Borval99/EBmetro/3D Model/Display Legno/Back.SLDPRT

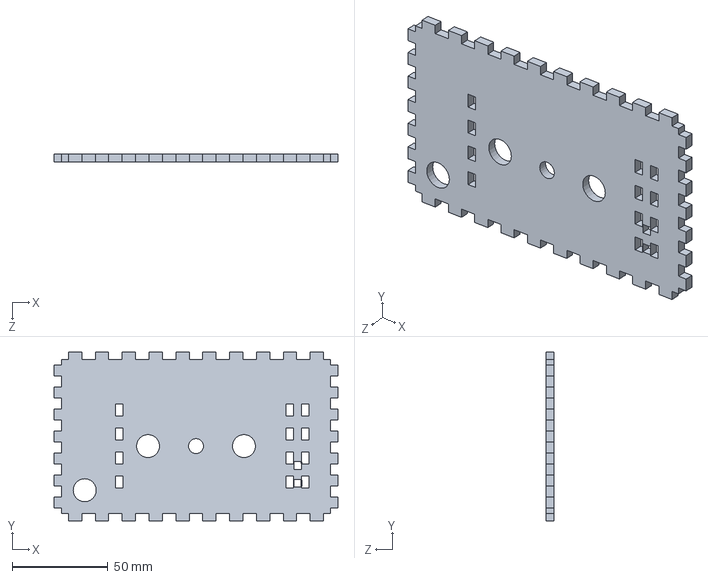
[picture p22: CAD file, 2026-04-02]
3D Model/Display Legno/Back.SLDPRT
148.0 x 88.0 x 4.00 mm
