Borval99/EBmetro/3D Model/Display/Encoder.SLDPRT

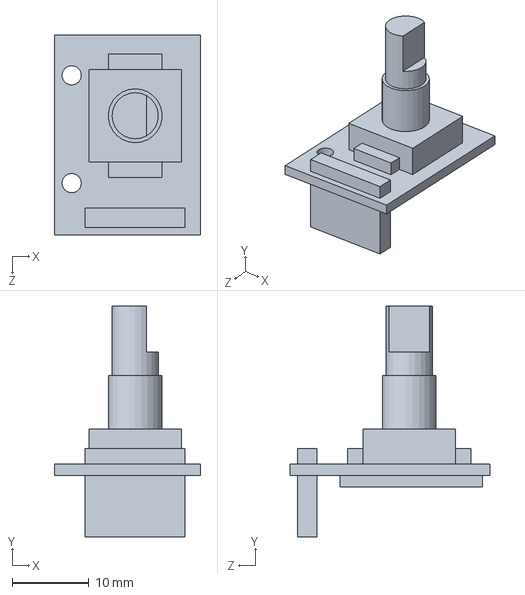
[picture p23: CAD file, 2026-04-02]
3D Model/Display/Encoder.SLDPRT
19.0 x 30.0 x 26.0 mm
