Borval99/EBmetro/3D Model/Display Legno/Left.SLDPRT

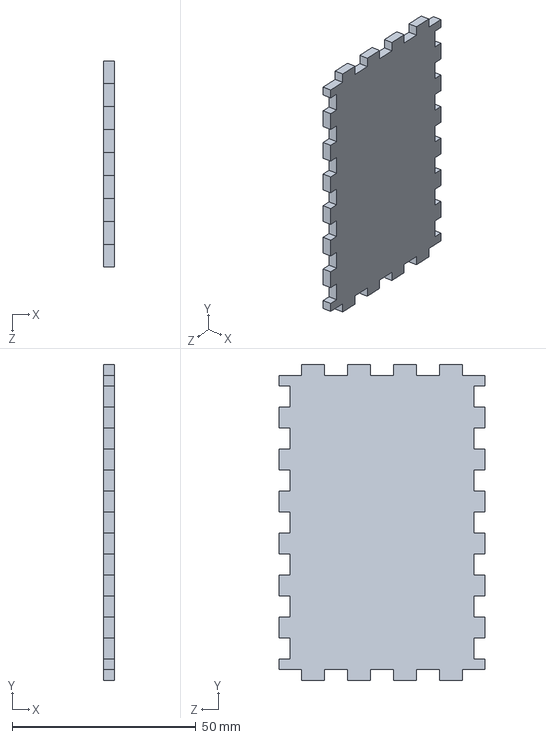
[picture p24: CAD file, 2026-04-02]
3D Model/Display Legno/Left.SLDPRT
3.00 x 86.0 x 56.0 mm
