Borval99/EBmetro/3D Model/Display/MKR1010WiFi.SLDPRT

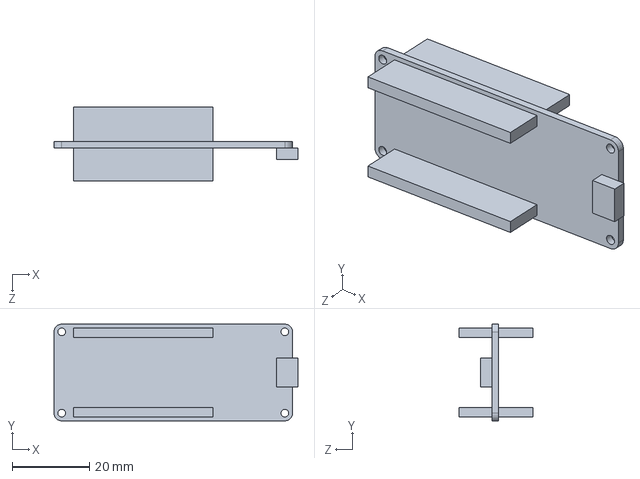
[picture p25: CAD file, 2026-04-02]
3D Model/Display/MKR1010WiFi.SLDPRT
63.0 x 25.0 x 19.2 mm
