Borval99/EBmetro/3D Model/Display Legno/RightV3.SLDPRT

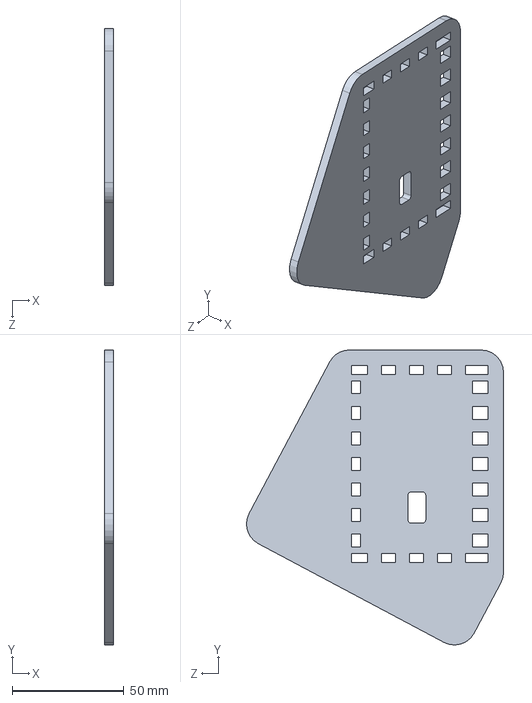
[picture p26: CAD file, 2026-04-02]
3D Model/Display Legno/RightV3.SLDPRT
4.00 x 132.0 x 115.1 mm
