Borval99/EBmetro/3D Model/Display/Case_Base.SLDPRT

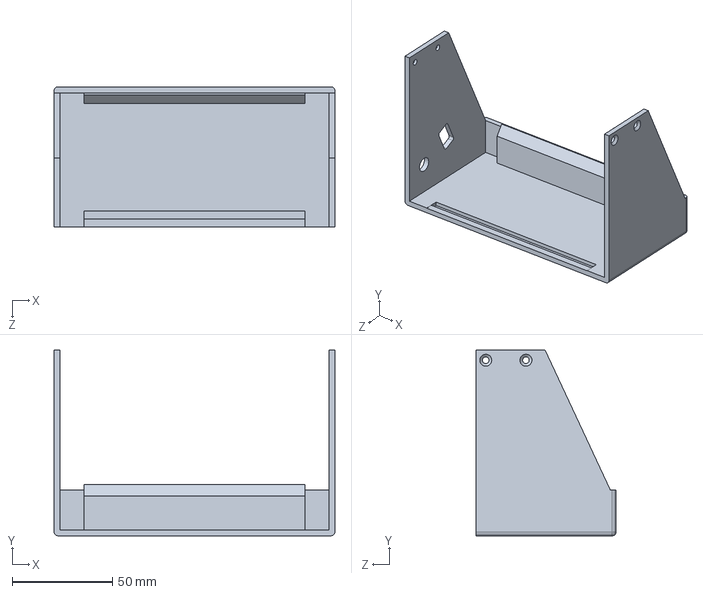
[picture p27: CAD file, 2026-04-02]
3D Model/Display/Case_Base.SLDPRT
140.0 x 92.5 x 70.0 mm
