Borval99/EBmetro/3D Model/Display Legno/Boccola_4.SLDPRT

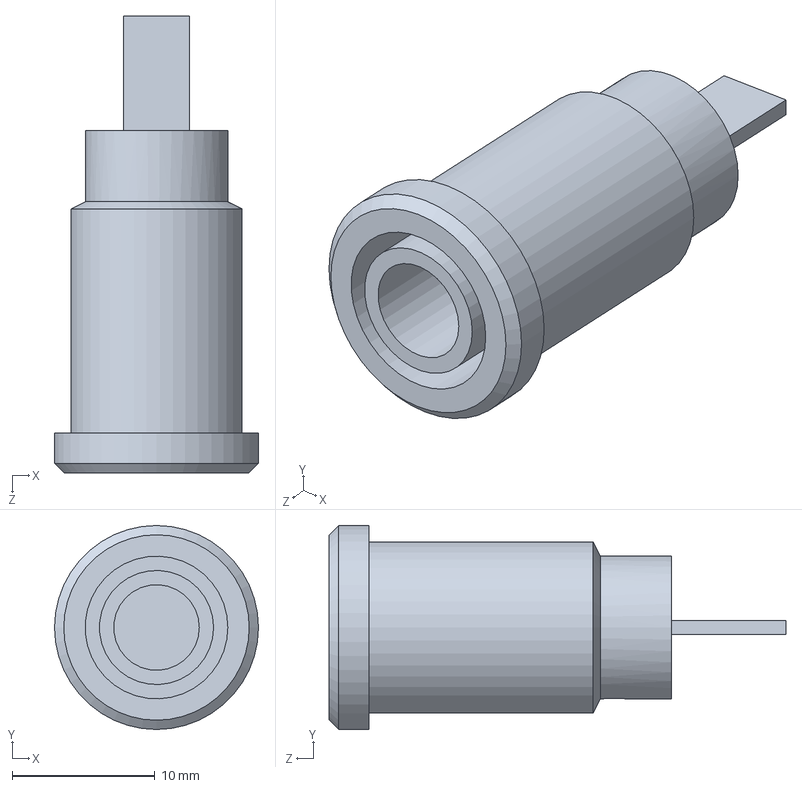
[picture p28: CAD file, 2026-04-02]
3D Model/Display Legno/Boccola_4.SLDPRT
14.3 x 14.3 x 32.0 mm
