Borval99/EBmetro/3D Model/Display Legno/Front.SLDPRT

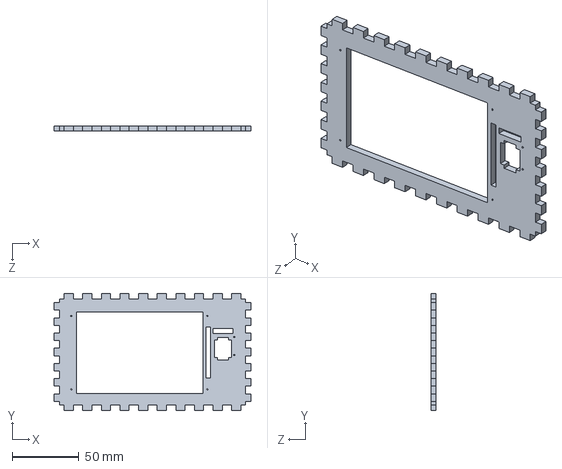
[picture p29: CAD file, 2026-04-02]
3D Model/Display Legno/Front.SLDPRT
148.0 x 88.0 x 4.00 mm
