Borval99/EBmetro/3D Model/Display Legno/Pirulino.SLDPRT

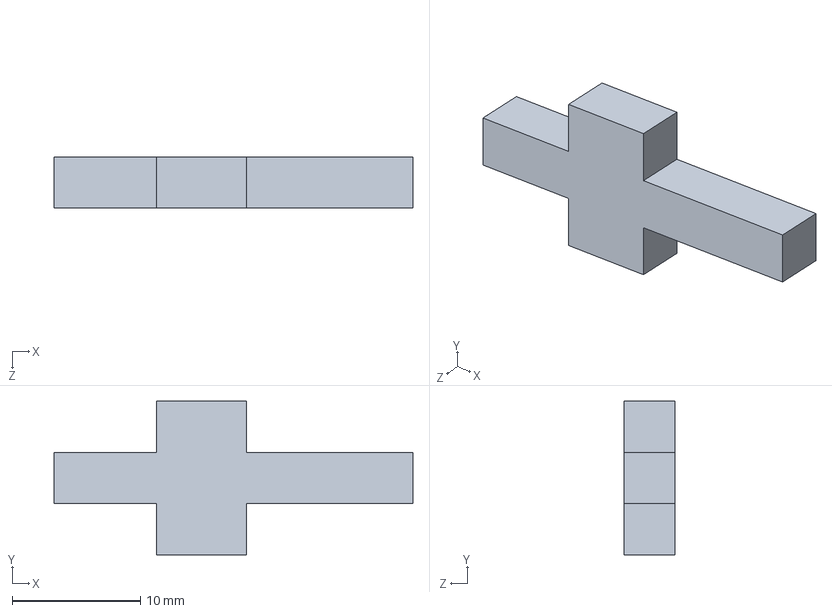
[picture p30: CAD file, 2026-04-02]
3D Model/Display Legno/Pirulino.SLDPRT
28.0 x 12.0 x 4.00 mm
