Borval99/EBmetro/3D Model/Display Legno/PW_Conn.SLDPRT

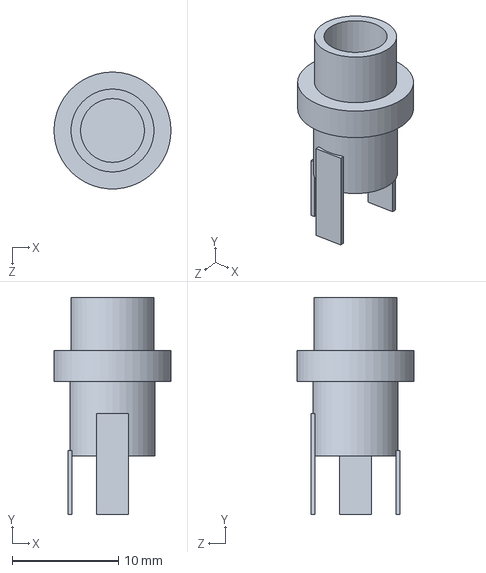
[picture p31: CAD file, 2026-04-02]
3D Model/Display Legno/PW_Conn.SLDPRT
11.0 x 20.4 x 11.0 mm
