Borval99/EBmetro/3D Model/Display Legno/Mask.SLDPRT

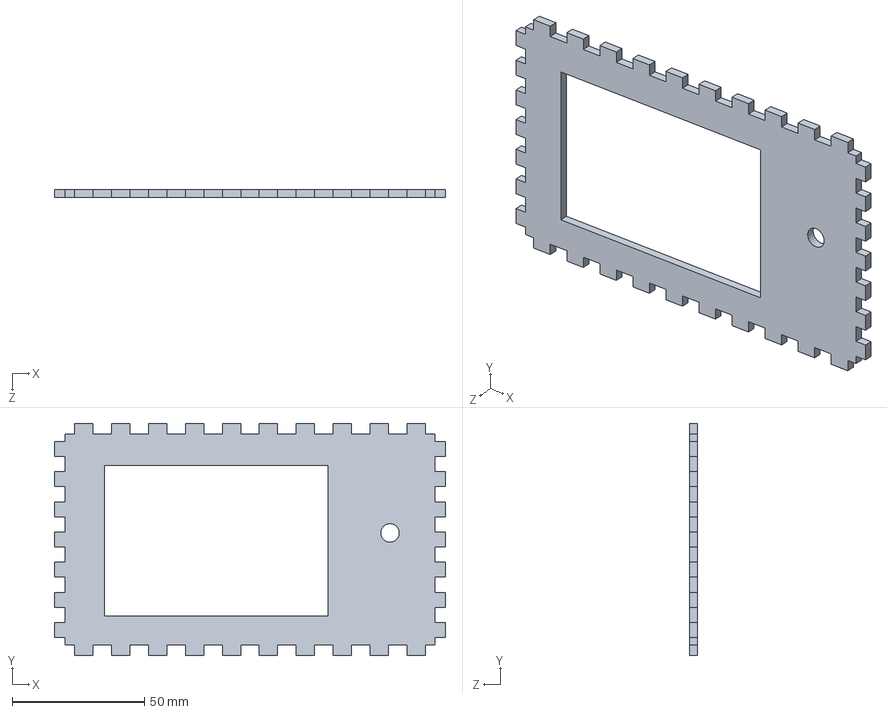
[picture p32: CAD file, 2026-04-02]
3D Model/Display Legno/Mask.SLDPRT
148.0 x 88.0 x 3.00 mm
