Borval99/EBmetro/3D Model/Display Legno/Supporto2.SLDPRT

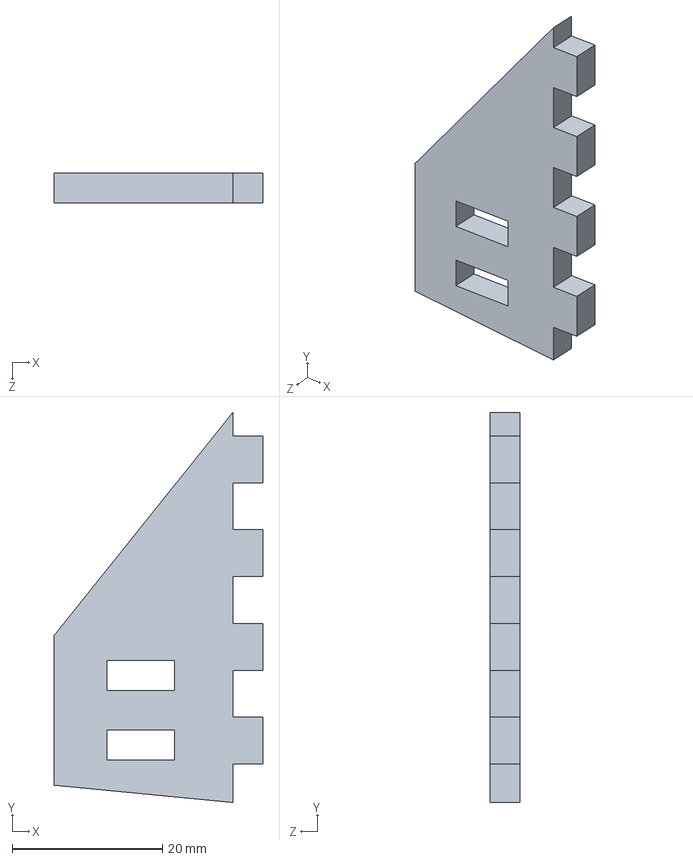
[picture p33: CAD file, 2026-04-02]
3D Model/Display Legno/Supporto2.SLDPRT
27.8 x 52.0 x 4.00 mm
