Borval99/EBmetro/3D Model/Display/QT-PY.SLDASM

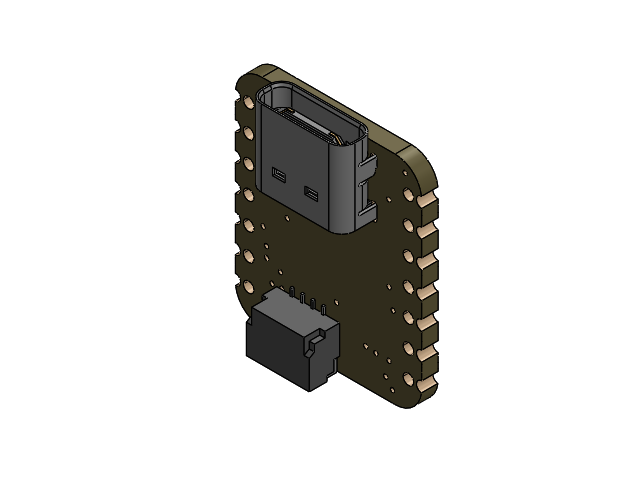
[picture p38: CAD file, 2026-04-02]
3D Model/Display/QT-PY.SLDASM
Board.step
STEMMA_I2C_QTSKINNY.step
USB Type C.step
