Borval99/EBmetro/3D Model/Display Legno/PCBB.SLDASM

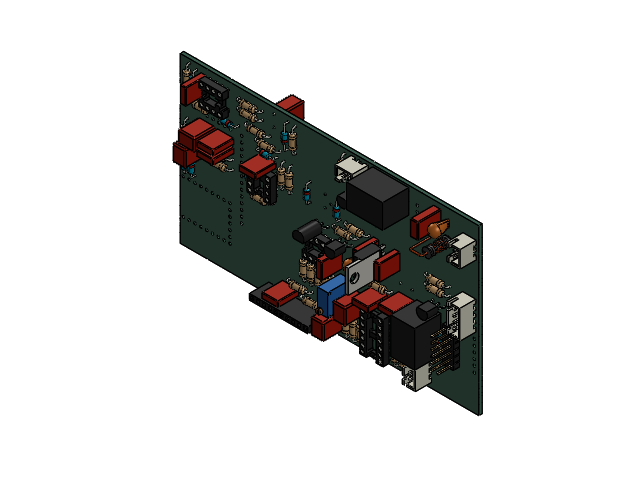
[picture p39: CAD file, 2026-04-02]
3D Model/Display Legno/PCBB.SLDASM
C_Rect_L7.2mm_W2.5mm_P5.00mm_FKS2_FKP2_MKS2_MKP2_2.step x 10
R_Axial_DIN0207_L6.3mm_D2.5mm_P10.16mm_Horizontal_1.step x 34
DIP-8_W7.62mm_Socket_2.step x 3
D_DO-35_SOD27_P7.62mm_Horizontal_2.step x 12
Potentiometer_Bourns_3296W_Vertical_2.step
TO-92L_Inline_Wide_2.step
PinSocket_1x10_P2.54mm_Vertical_2.step
JST_XH_B2B-XH-A_1x02_P2.50mm_Vertical_2.step x 2
PinHeader_2x06_P2.54mm_Vertical_2.step
TO-220-3_Vertical_2.step
C_Rect_L7.2mm_W5.5mm_P5.00mm_FKS2_FKP2_MKS2_MKP2_2.step x 6
Relay_SPDT_HJR-4102_2.step x 2
TO-92_Inline_Wide_2.step x 3
JST_XH_B3B-XH-A_1x03_P2.50mm_Vertical_2.step
C_Rect_L7.0mm_W3.5mm_P5.00mm_2.step
JST_XH_B4B-XH-A_1x04_P2.50mm_Vertical_2.step
DIP-14_W7.62mm_Socket_2.step
CP_Radial_Tantal_D5.0mm_P2.50mm_2.step x 2
L_Axial_L9.5mm_D4.0mm_P5.08mm_Vertical_Fastron_SMCC_2.step
D_DO-35_SOD27_P10.16mm_Horizontal_2.step
Display_EBmetro_PCB_2.step
