Borval99/EBmetro/EBmetro/Circuit/Display_EBmetro.asc

C2: cap; 100n
C3: cap; 100n
C4: cap; 1µ
C5: cap; 1µ
C6: cap; 100n
C7: cap; 100n
C8: cap; 100n
C9: cap; 100n
C10: cap; 1µ
C11: cap; 100n
C12: cap; 100n
C13: cap; 15µ
C14: cap; 15n
C15: cap; 1µ
C16: cap; 15µ
C17: cap; 100n
C18: cap; 100n
C19: cap; 1m
C20: cap; 1m
D1: diode; 1N4148
D2: diode; 1N4148
D3: diode; 1N4148
D6: diode; 1N4148
D7: diode; 1N4148
D8: diode; 1N4148
D9: diode; 1N4148
D10: diode; 1N4148
D11: diode; 1N4148
D12: diode; 1N4148
D13: diode; 1N4148
D14: diode; 1N4148
D15: zener; D 2V5 Zener
MCP1: OpAmp_
MCP2: OpAmp_
MCP3: OpAmp_
MCP4: OpAmp_
MCP5: OpAmp_
MCP6: OpAmp_
MCP7: OpAmp_
MCP8: OpAmp_
MCP9: OpAmp_
MCP10: OpAmp_
Q1: npn; BC547B
Q2: npn; BC547B
Q3: npn; BC547B
R1: res; 2.4k
R2: res; 470
R3: res; 680
R4: res; 3.3k
R5: res; 33k
R6: res; 3.3k
R7: res; 10Meg
R8: res; 10k
R9: res; 33k
R10: res; 330k
R11: res; 10k
R12: res; 3.3k
R13: res; 33k
R14: res; 10k
R15: res; 10k
R16: res; 3.3k
R17: res; 33k
R18: res; 150
R19: res; 100
R20: res; 1k
R21: res; 4.53k
R22: res; 18k
R23: res; 100
R24: res; 45.3k
R25: res; 45.3k
R26: res; 45.3k
R27: res; 45.3k
R28: res; 45.3k
R29: res; 45.3k
R30: res; 220k
R31: res; 15k
U1: LM336Z_2_5
U2: pot_
U3: rly_spdt
U4: rly_spdt
Named nets: VREF_2_5V, 5V_VDD, 0, PowerON_Motor, Pin_PowerOn_Motor, A2_ADC, I2C_Internal_SCL, I2C_Internal_SDA, 12V_VDD_INPUT, SW_PIN_RP2040, 3V3_VDD, T_IRQ_PIN_RP2040, DT_PIN_RP2040, CLK_PIN_RP2040, VREF_2_5V_ZENER, SW_PIN, DT_PIN, CLK_PIN, T_IRQ_PIN, T_DO_PIN, T_DIN_PIN, T_CS_PIN, T_CLK_PIN, SDO_PIN, LED_PIN, SCK_PIN, SDI_PIN, DC_RS_PIN, RESET_PIN, CS_PIN, Pin_Comando_Condensatore, Alert_ADC_PIN, A0_ADC
MCP602_0_2/2
EbMetro +
EbMetro -
Schermatura
1
2
3
2
1
2
1
5V
GND
3V3
29
28
27
26
15
14
13
12
11
10
9
4
5
6
7
8
0
1
2
3
T_IRQ
T_DO
T_DIN
T_CS
T_CLK
SDO
LED
SCK
SDI
DC/RS
RESET
CS
GND
VCC
CLK
DT
SW
+
GND
Gestione Power On Motore
ASSICURARSI CHE SIA SUL PIN NA
MCP602_0_1/2
ADS1115 per DCDC
VDD
GND
SCL
SDA
ADDR
ALRT
A0
A1
A2
A3
Alimentazione 12V Esterna
Modulo DCDC
MCP602_1_2
MCP602_1_1/2
MCP602_2_2
MCP602_2_1/2
ENCODER
DISPLAY
RP2040
VREF 2.5V
Circuito protezione per EBmetro
Trigger di Schmitt per i 3 pin dell'encodere e per l'IRQ del Touch
MCP602_3_1/2
MCP602_3_2/2
MCP602_4_1/2
MCP602_4_2/2
