Borval99/EBmetro/EBmetro/Circuit/Trigger.asc

C1: cap; 100n
D2: diode; 1N4148
R1: res; 3.3k
R2: res; 33k
R3: res; 56
R4: res; 330k
R5: res; 10k
U2: MCP601_AB
V1: voltage; 3.3
V2: voltage; 2.5
V3: voltage; SINE(1.7 1.6 5)
Named nets: 0, PIN_RP2040
.tran 0.5
