Borval99/EBmetro/Generatore/Circuit/Case/Case_Circuit_RP2040.asc

C1: cap; 100n
C2: cap; 10n
C3: cap; 10n
C4: cap; 100n
C5: cap; 100n
C6: cap; 10n
C13: cap; 100n
C14: cap; 100n
C15_tantalio: polcap; 10µ
D1: diode; 1N4148
D2: diode; 1N4148
D3: diode; 1N4148
D4: diode; 1N4148
D7: diode; 1N4148
D8: diode; 1N4148
D9: diode; 1N4148
D10: diode; 1N4148
D11: diode; 1N4148
D12: diode; 1N4148
L1: ind; 100µ
M1: nmos; 2N7000
MCP1: OpAmp_
MCP2: OpAmp_
MCP3: OpAmp_
MCP602: OpAmp_
Plastico: cap; 15µf
Q1: npn; BC547B
Q2: npn; BC547B
R1: res; 2.4k
R2: res; 100
R3: res; 100
R4: res; 14.7k
R5: res; 14.7k
R6: res; 45.3k
R7: res; 45.3k
R8: res; 27k
R9: res; 3k
R10: res; 100
R10_100W: res; 0.1
R11: res; 1k
R11_100W: res; 0.1
R12: res; 10k
R12_100W: res; 0.1
R13: res; 10k
R13_100W: res; 0.5
R14_100W: res; 0.5
R18: res; 1.2k
R19: res; 10k
R20: res; 10k
R21: res; 10k
R22: res; 4.7k
R23: res; 4.7k
R24: res; 4.7k
R25: res; 75
R26: res; 4.7k
R27: res; 4.7k
R28: res; 4.7k
Shunt_Resistor_1: res2; 1,875m
U1: LM336Z_2_5
U2: pot_
U3: LM336Z_2_5
U4: pot_
U8: rly_spdt
U9: LMC6484IN
Named nets: VREF_2_5V, 0, Input_Shunt+, Input_Shunt-, 5V_VDD, A2_ADC, A1_RP2040, Input_V+_DCDC, 3V3_VDD, Level_Shift_Low_TX, I2C_external_Low_SDA, I2C_external_High_SCL, 230VAC, 5V_VDD_OUT, SA50_30A, SA50_15A, DCDC_MAIN, SA50_GND, Pin_Current_DCDC+, PowerON_DCDC+, PowerON_DCDC-, Pin_PowerOn_DCDC, DCDC_24V+, OUTPUT_DCDC_Wire, A0_RP2040, PWM_PIN_4_5_6_7, 13V_VDD_Ventole, I2C_Internal_Low_SDA, Level_Shift_High_TX, Level_Shift_High_RX, Level_Shift_Low_RX, I2C_external_Low_SCL, I2C_external_High_SDA, I2C_Internal_Low_SCL, I2C_Internal_High_SDA, I2C_Internal_High_SCL, VREF_5V, LM35_PCB, LM35_NANO, LM35_DCDC, LM35_Dissipatore, LM35_Alimentatore, PWM_Ventola_IN, PWM_Ventola_OUT, PWM_Ventola_Dissipatore, PWM_Ventola_DCDC, A2_RP2040, PIN15_Alert_Low_1, PIN15_Alert_Low_0, PIN15_Alert_High_0, PIN15_Alert_High_1
Alimentazione Interna
Lettura della Tensione in uscita, riduce la tensione letta di 1/10
Lettura della tensione sulla resistenza di Shunt moltiplicata per x3.081633
Tensione di riferimento 2.49V
l'Opamp MCP602 necessita di un condensatore vicino, sull'alimentazione
ADS1115_0 per DCDC
VDD
GND
SCL
SDA
ADDR
ALRT
A0
A1
A2
A3
Level Shifter
HV
LV
GND
GND
LV1  LV2
LV3  LV4
HV1  HV2
HV3  HV4
Alimentazione
GX 12 Connettore Manico
GX 12 Connettore Display
Sensing e Load Esterni
CASE
MCP4725 DAC 12Bit per DCDC
OUT
GND
SCL
SDA
VCC
GND
Gestione Power On DCDC
Alimentazione Esterna
Alimentazione DCDC Esterno
PWM Ventole x4
Level Shifter
HV
LV
GND
GND
LV1  LV2
LV3  LV4
HV1  HV2
HV3  HV4
TOP VIEW
1
2
3
1
2
1
2
1
2
ASSICURARSI CHE SIA SUL PIN NC
MCP602_1/2
MCP602_2/2
MCP602_2/2
MCP602_1/2
l'Opamp MCP602 necessita di un condensatore vicino, sull'alimentazione
Alimentazione per l'MCP4725
Qui ci va l'LM336-5.0
Ha la stessa piedinatura
Tagliare i ponti sotto l'MCP4725
TOP VIEW
1
2
3
Da mettere 3 connettori, un lm35 è on-board
5V
GND
3V3
29
28
27
26
15
14
13
12
11
10
9
4
5
6
7
8
0
1
2
3
ADS1115_1 per DCDC
VDD
GND
SCL
SDA
ADDR
ALRT
A0
A1
A2
A3
RP2040
