Borval99/EBmetro/Generatore/Circuit/Display_Case/Display_Case.asc

C2: cap; 100n
C3: cap; 100n
C4: cap; 100n
C5: cap; 100n
C6: cap; 10n
C7: cap; 10n
C8: cap; 100n
C12: cap; 100n
D6: diode; 1N4148
D7: diode; 1N4148
D8: diode; 1N4148
D9: diode; 1N4148
D15: zener; D 2V5 Zener
MCP3: OpAmp_
MCP4: OpAmp_
MCP5: OpAmp_
MCP6: OpAmp_
R4: res; 3.3k
R5: res; 33k
R6: res; 3.3k
R8: res; 10k
R9: res; 33k
R10: res; 330k
R11: res; 10k
R12: res; 3.3k
R13: res; 33k
R16: res; 3.3k
R17: res; 33k
R18: res; 150
Named nets: 5V_VDD, 0, SW_PIN_RP2040, 3V3_VDD, T_IRQ_PIN_RP2040, DT_PIN_RP2040, CLK_PIN_RP2040, VREF_2_5V_ZENER, SW_PIN, DT_PIN, CLK_PIN, T_IRQ_PIN, T_DO_PIN, T_DIN_PIN, T_CS_PIN, T_CLK_PIN, SDO_PIN, LED_PIN, SCK_PIN, SDI_PIN, DC_RS_PIN, RESET_PIN, CS_PIN, Level_Shift_Low_TX, Level_Shift_High_TX, Level_Shift_High_RX, Level_Shift_Low_RX, 13V_VDD
5V
GND
3V3
29
28
27
26
15
14
13
12
11
10
9
4
5
6
7
8
0
1
2
3
T_IRQ
T_DO
T_DIN
T_CS
T_CLK
SDO
LED
SCK
SDI
DC/RS
RESET
CS
GND
VCC
CLK
DT
SW
+
GND
Alimentazione 12V Esterna
Modulo DCDC
MCP602_1_2
MCP602_1_1/2
MCP602_2_2
MCP602_2_1/2
ENCODER
DISPLAY
RP2040
VREF 2.5V
Trigger di Schmitt per i 3 pin dell'encodere e per l'IRQ del Touch
Level Shifter
HV
LV
GND
GND
LV1  LV2
LV3  LV4
HV1  HV2
HV3  HV4
GX 12 Connettore Display
TOP VIEW
