Borval99/EBmetro/Generatore/Circuit/Manico/Manico.asc

C2: cap; 10n
C3: cap; 1n
C4: cap; 1n
C5: cap; 10µ
C6: cap; 100n
C7: cap; 100n
C8: cap; 100n
C9: cap; 100n
D3: diode; 1N4148
D4: diode; 1N4148
MCP1: OpAmp_
Q1: npn; BC547B
R2: res; 200
R3: res; 56k
R4: res; 100
R5: res; 100
R6: res; 2.4k
R7: res; 100
R8: res; 1k
U1: AD623
U5: LM336Z_2_5
U6: pot_
Named nets: Input_coil-, Input_coil+, 0, VREF_2_5V, 5V_VDD, A2_ADC, ADS1115_I2C, 5V_VDD_OUT
Manico
Tensione di riferimento 2.5V
l'Opamp LMC6484 necessita di un condensatore vicino, sull'alimentazione
ADS1115
VDD
GND
SCL
SDA
ADDR
ALRT
A0
A1
A2
A3
AD623  guadagno pari a 500 sulla spira
GX 12 Connettore Manico
MCP602_0_2/2
